deniskokarev/geiger/hardware/geiger_shield.asc

C1: cap; .005µ
D1: diode
L1: ind; 10m
Q1: npn
Q2: npn; 2N3904
Q3: npn; 2N3904
R1: res; 1e7
R2: res; 5e9
R3: res; 100k
R4: res; 10
R5: res; 50
R6: res; 10k
R7: res; 7k
R8: res; 1e6
R9: res; 100
U1: OP777
V1: voltage; 3.3
V2: voltage; PULSE(0 3 0 0 0 .45m .5m)
Named nets: 0, VCC, CTL, HI, MEA
*
.lib opamp.sub
.tran .1m 3
