deniskokarev/geiger/firmware/Core/Inc/RTE_Components.h

/**
  ******************************************************************************
  * @file
  * @author  MCD Application Team
  * @version V2.0.0
  ******************************************************************************
  * @attention
  *
  * COPYRIGHT(c) 2022 STMicroelectronics
  *
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
  */
  /* Define to prevent recursive inclusion -------------------------------------*/
#ifndef  __RTE_COMPONENTS_H__
#define  __RTE_COMPONENTS_H__

/* Defines ------------------------------------------------------------------*/
/* STMicroelectronics.X-CUBE-BLE1.6.2.3 */
#define SENSOR_DEMO_BS
#define HCI_TL
#define HCI_TL_INTERFACE

#endif /* __RTE_COMPONENTS_H__ */
